Jazor25/esphome-tv-fan-project/img/installed_case_open.jpg

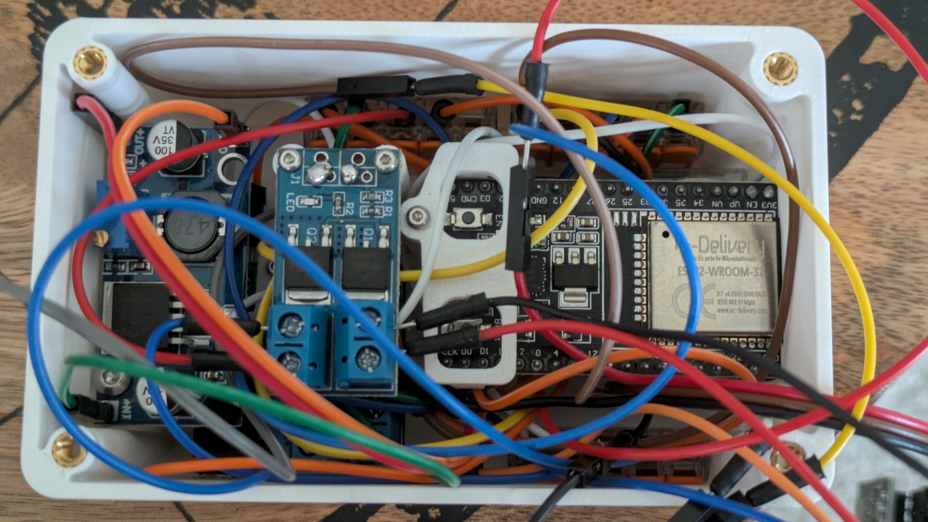
img/installed_case_open.jpg
