Jazor25/esphome-tv-fan-project/img/partially_installed_case_open_2.jpg

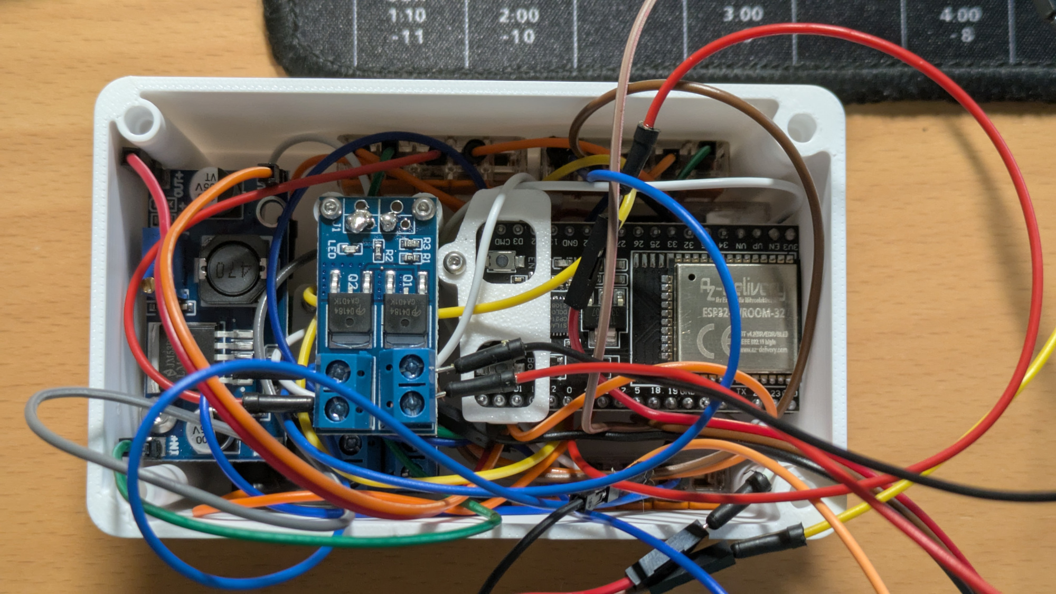
img/partially_installed_case_open_2.jpg
