Jazor25/esphome-tv-fan-project/img/prototype_setup.jpg

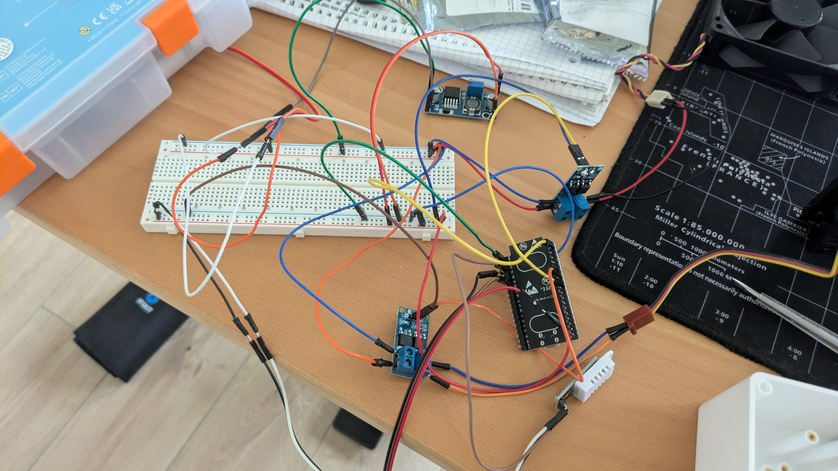
img/prototype_setup.jpg
